solarpunklab/coxy/COXY-KONTROL/data/lighting.png

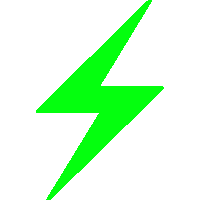
COXY-KONTROL/data/lighting.png
