solarpunklab/coxy/images/chatgpt.png

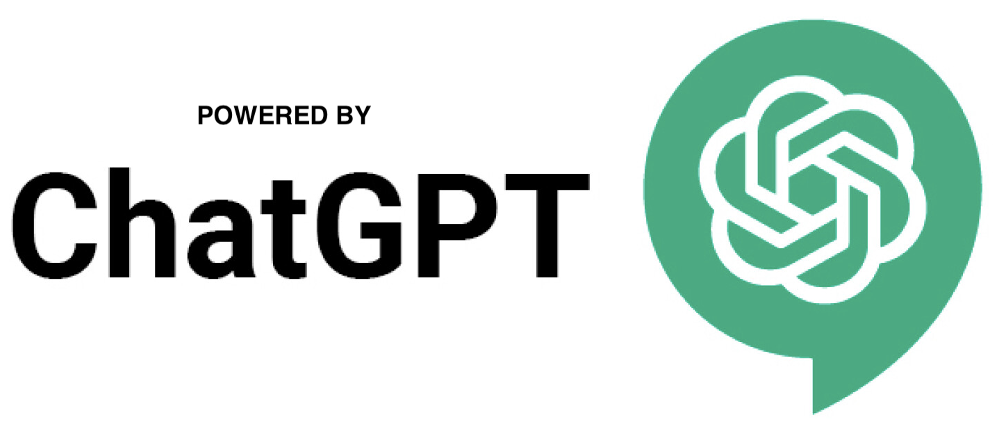
images/chatgpt.png
