solarpunklab/coxy/images/code-filesystem.png

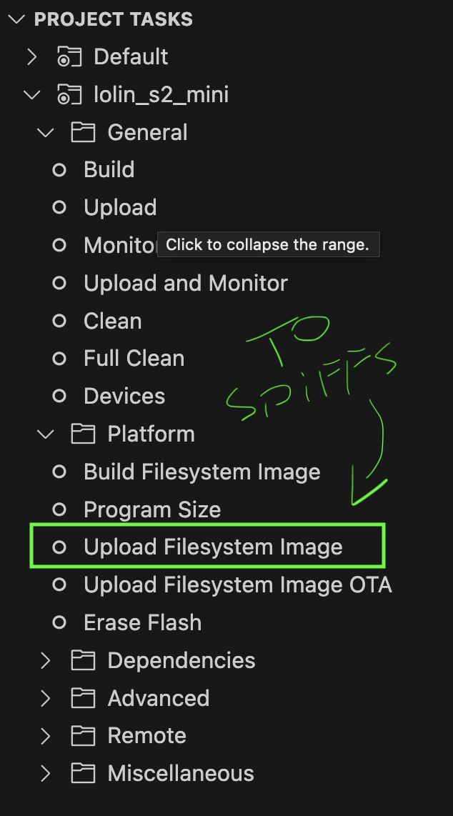
images/code-filesystem.png
