solarpunklab/coxy/images/code-wifi.png

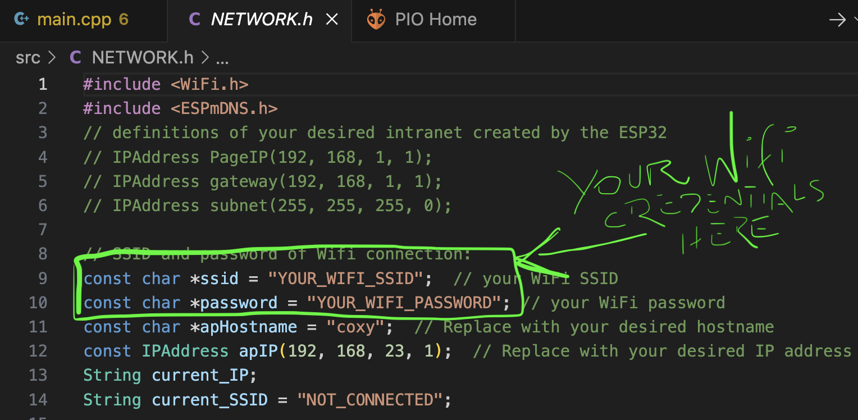
images/code-wifi.png
