solarpunklab/coxy/images/coxy-wifi-motor.png

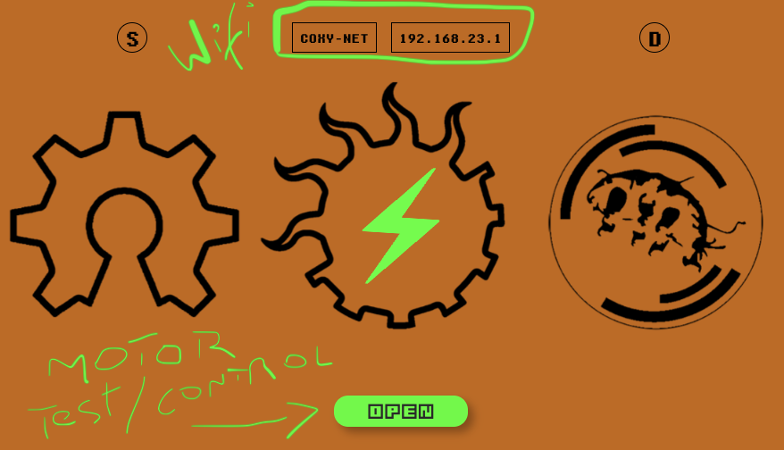
images/coxy-wifi-motor.png
