solarpunklab/coxy/images/datalog-win.jpg

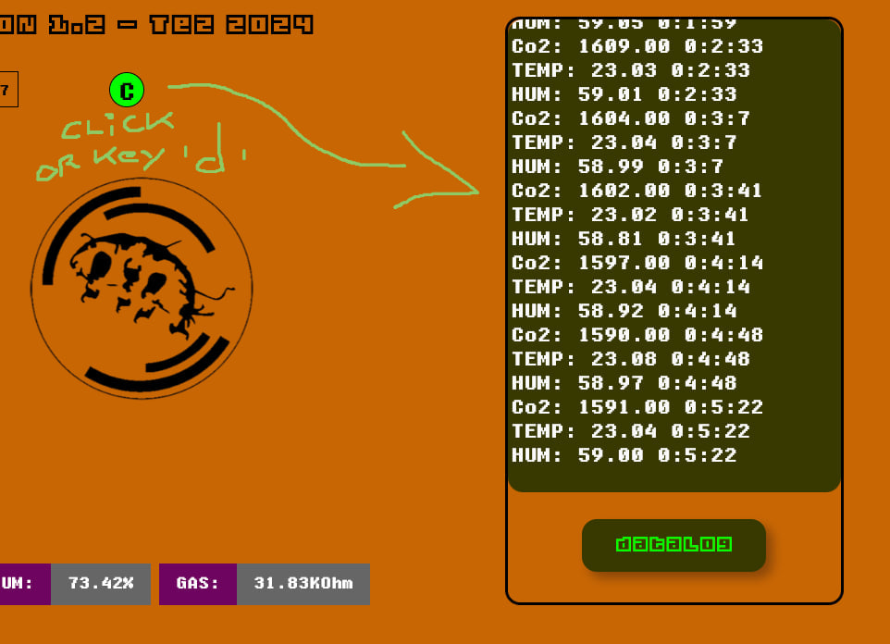
images/datalog-win.jpg
