solarpunklab/coxy/images/src-hackteria-gosh.jpg

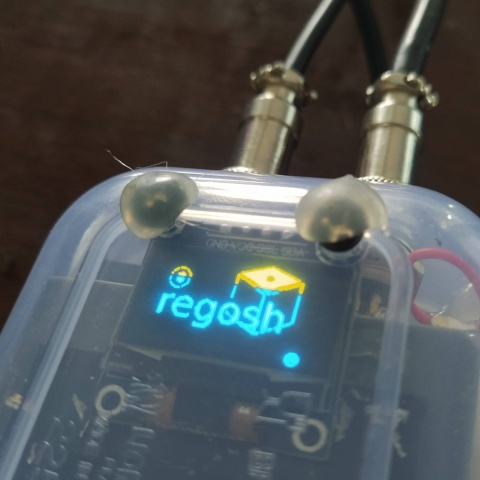
images/src-hackteria-gosh.jpg
