solarpunklab/coxy/images/tez-src-guts.jpeg

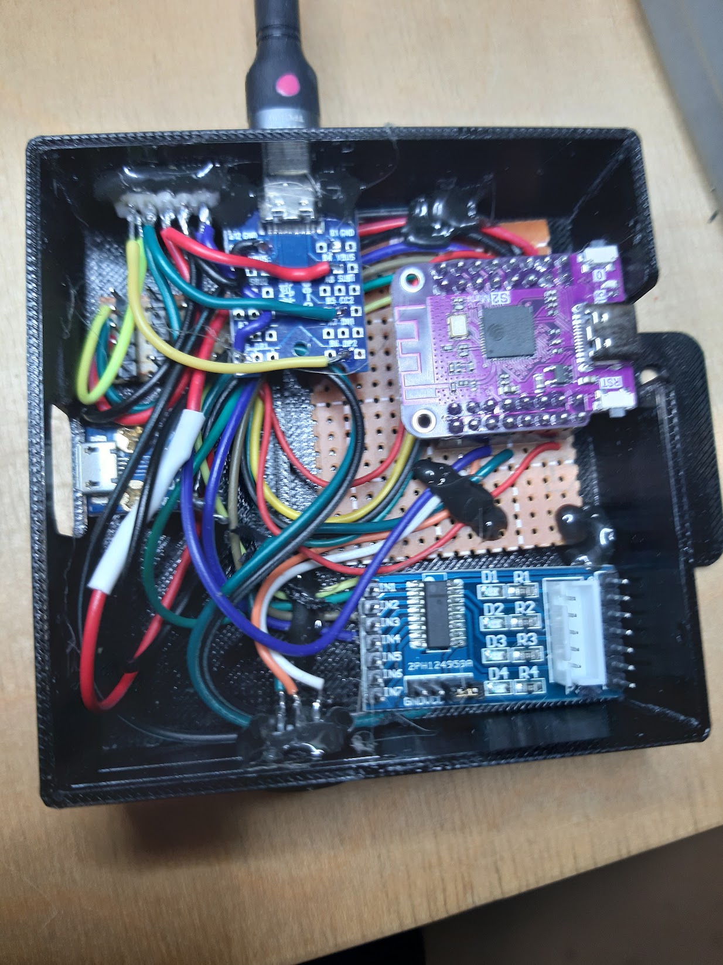
images/tez-src-guts.jpeg
