solarpunklab/coxy/images/tez-src-v1-a.png

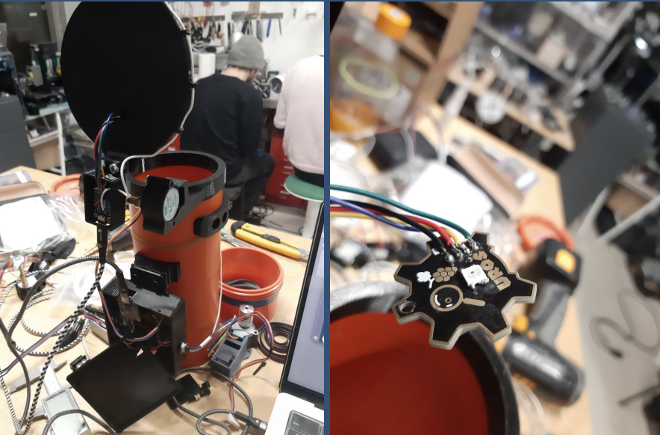
images/tez-src-v1-a.png
