solarpunklab/coxy/images/tez-src-v1-c.png

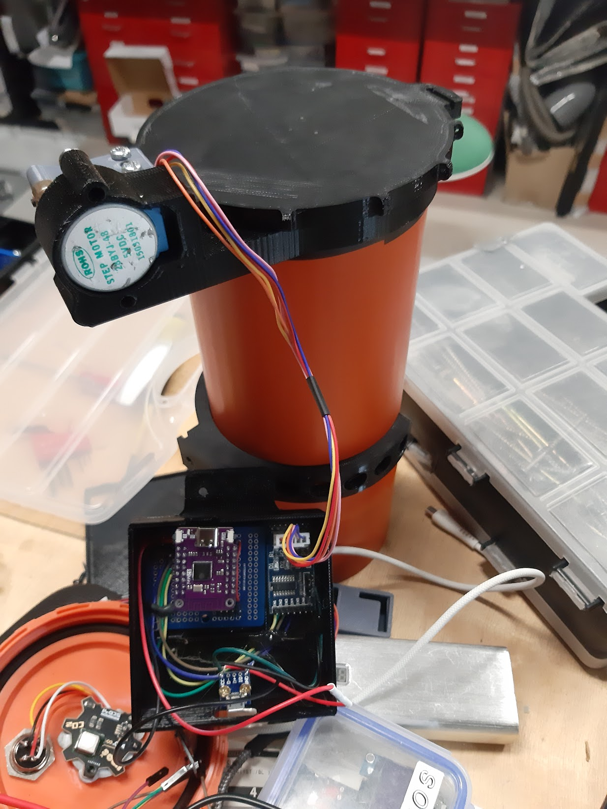
images/tez-src-v1-c.png
